Bongorian/mb4-independent-bass-bridge/revisions/B/pdf/MB4_design_and_drawings.pdf

# MB4 — 4弦独立サドルレス・ブリッジ

ジャズベ／プレベ想定。汎用M3ステンレス金物と、3種類の切削部品で構成。

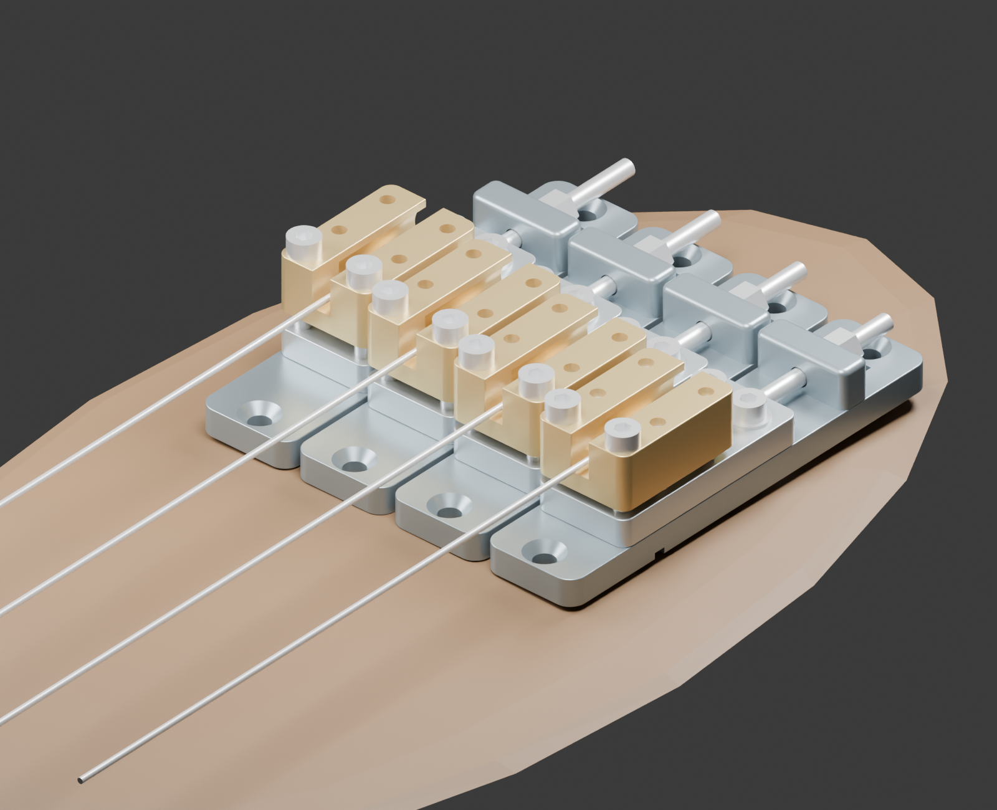
[picture p12: figure]

MB4 | Rev B | 2026-10-05 | 単位 mm | 試作・見積用 | 1 / 9

4個のモジュールを19 mmピッチで配置

ベース幅18 mm／全体幅75 mm

ベース奥行82 mm（ねじ棒は最大Y=90）

弦軸の参考高さ15〜20 mm

キャリッジ移動12 mm／各弦独立

裏面：φ12.5 × 深さ1.5のピエゾ用窪み

B01 固定ベース：A6061-T6 ×4

C01 キャリッジ：A6061-T6 ×4

A01 アンカー：C3604黄銅 ×4

外周R2〜R3／後壁上面R1。

3軸切削＋反転＋側面の穴加工。

M3ねじ穴はSTEPでは下穴径を表現。

図面のねじ指示を加工時に適用。

既存5穴には非互換。弦間・弦高・ボディ端までの余白を実機で確認して新規取付。

球状／筒状ボールの形・巻き方に応じて実弦で支点を確認。音質・分離度は未検証。

# B01 / 固定ベース

数量4 | A6061-T6 | 18 × 82 × 12、板厚5 | 外周R3、外周稜線R0.2、後壁は9ページ参照

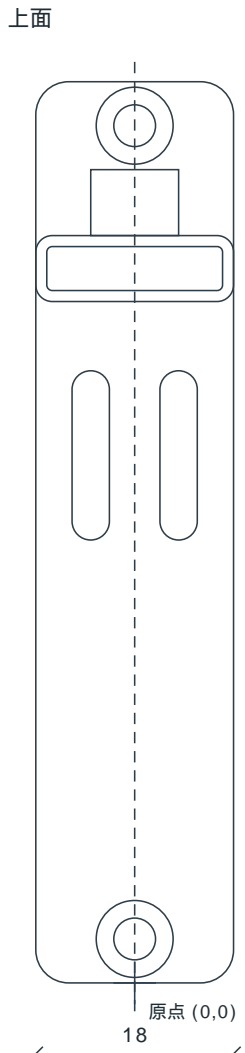
[picture p13: figure]
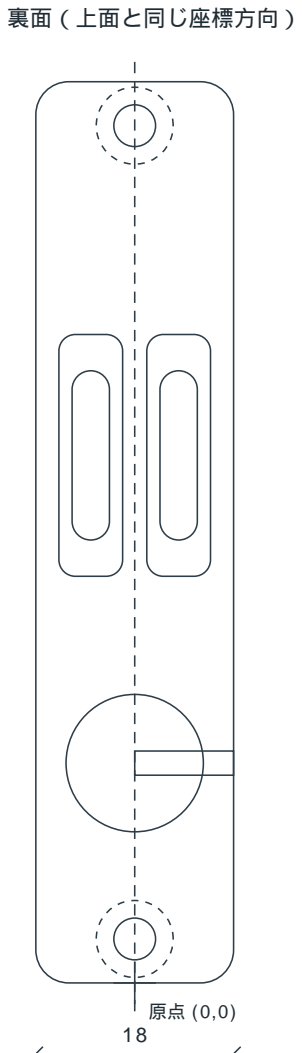
[picture p14: figure]
裏面（上面と同じ座標方向）

基準：X=幅中心、Y=前端、Z=ボディ面。

取付穴：(0,4)、(0,78)／φ3.8貫通。

皿座：上面φ7、90°、深さ1.6。

長穴中心：X=±4、Y=48。

長穴：幅3.4、全長15.4、貫通。

裏側ナット溝：5.8 × 22 × 深さ2.2。

同中心、四隅R1.5。裏面から切削。

ピエゾ窪み：(0,20)、φ12.5、深さ1.5。

配線溝：X=0〜9、Y=18.9〜21.1。

裏面から深さ1.2、右側面に開放。

後壁：Y=62〜68、Z=5〜12、幅18。

後壁穴：X=0、Z=7.5、φ3.4 Y方向貫通。

金物逃げ：X=±4、Y=68〜74。

上面から深さ1.5（底Z=3.5）。

側面（Y-Z）

82

# C01 / キャリッジ

数量4 | A6061-T6 | 18 × 40 × 5 | 外周R2、外周の上下稜線R0.2 | 穴位置・支持面高さは維持

上面

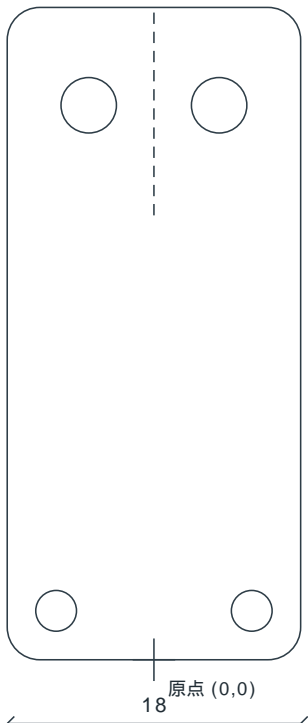
[picture p15: figure]

側面（Y-Z）

40

後面（X-Z）

基準：X=幅中心、Y=キャリッジ前端、Z=下面。

アンカー固定用：(±6,3)、M3 × 0.5 貫通、2箇所。

移動固定用：(±4,34)、φ3.4 貫通、2箇所。

後面ねじ：X=0、Z=2.5、Y方向 M3 × 0.5。

有効ねじ深さ10以上。φ2.5の円筒下穴深さ12＋ドリル先端0.75。

CADの後面穴は下穴形状。止めねじではなく張力受けのねじ棒を固定。

後面穴軸から上下面まで2.5。タップ後の残り肉は約1 mm。

ベース上の固定ねじ：M3 × 10 + 厚さ0.5ワッシャ + DIN562薄形四角ナット。

ナット5.5角 × 厚さ1.8。穴軸はベースのY=42〜54を移動。裏側溝に先にナットを入れる。

# A01 / ボールエンド・アンカー

数量4 | C3604快削黄銅 | 18 × 26 × 10 | 外周R2、外周上下稜線R0.2、スリット上縁R0.2

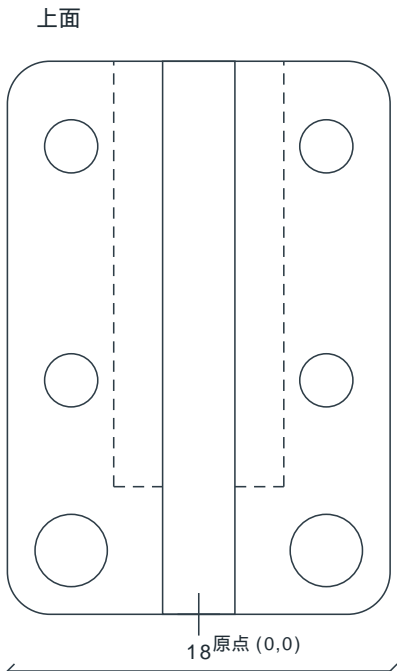
[picture p16: figure]

側面（Y-Z）

座面まで6

穴深さ20

後面（X-Z）

基準：X=幅中心、Y=前端、Z=下面。後面穴：X=0、Z=5、φ8、Y=26から深さ20。

開放スリット：幅3.4、全長26、底Z=3.3。上面から深さ6.7（R1.7端の工具逃げは部品外）。

高さ調整： (±6,11)、(±6,22)、4 × M3 × 0.5 貫通。保持ねじ：(±6,3)、2 × φ3.4 貫通。

ボールは後方から挿入し、Y=6の穴底肩で保持。弦は前方に水平に出す。後方穴は塞がない。

参考ボール外径6、厚さ4.75を仮定。最小厚さ3.8以上が条件。実弦で抜け・噛み込みを確認。

弦と巻き部分がスリット底・側壁に触れる場合はサドルレス条件が成立しない。最初の1個で検証。

# 組立断面・調整

弦高はネック／ボディの現物寸法と照合。弦を緩めて調整し、固定ねじは最後に締める。

中央模式図（Y-Z）：表示状態 q=14、g=2、参考弦軸H=17

← ナット側（前） | 後 →

ボディ面 Z=0

参考支点Y=q+6

裏面ピエゾの参考外形

窪みφ12.5 × 深さ1.5

参考素子φ12 × 厚さ0.7

接着・配線込みで1.2以下

金属面への短絡を防ぐ

ボディで素子を圧迫しない

前後調整：キャリッジ前端 q=8〜20。支点目安Y=14〜26。後ろのM3ナットで位置を合わせ、

四角ナットを使う上側2本のM3 × 10でキャリッジを固定。後ろの2個のナットをジャムロック。

高さ調整：4本のM3 × 10平先止めねじで隙間 g=0〜5。前後左右をそろえて、傾斜を抑える。

アンカー保持：2本のM3ボルトを下のキャリッジへ固定。底突きさせないため、次の金物を選ぶ。

g=0〜1未満：M3 × 16 + 厚さ1.0ワッシャ（0.5を2枚）。ねじ込み4〜5。

g=1〜3：M3 × 16、ワッシャなし。ねじ込み3〜5。

g=3超〜5：M3 × 20 + 厚さ2.0ワッシャ（0.5を4枚）。ねじ込み3〜5。

キャリッジの厚さは5。ボルト先端が下面を越えないことを組立時に確認。寸法公差分の余裕を取る。

# 部品表・加工指示

発注はB01／C01／A01の個別STEPとこのPDFをセットで。試作1弦分→実弦確認→4弦分が推奨。

B01 | 固定ベース A6061-T6 | | 18×82×12
C01 | キャリッジ A6061-T6 | | 18×40×5
A01 | アンカー C3604 | | 18×26×10
H01 | M3×10 平先 六角穴付き止めねじ SUS | 16 | 高さ調整
H02 | M3×16 六角穴付きボルト SUS | | アンカー保持 g<=3
H03 | M3×20 六角穴付きボルト SUS | 8予備 | アンカー保持 g>3
H04 | M3×10 六角穴付きボルト SUS | | キャリッジ固定
H05 | M3 DIN562 薄形四角ナット SUS | | 5.5角×厚さ1.8
H06 | M3全ねじ棒 SUS、長さ40 | | キャリッジへ10ねじ込む
H07 | M3六角ナット SUS | | 後面調整＋ジャムロック
H08 | M3平座金 φ7×厚さ0.5 SUS | 12 | 固定用8、後面用4
H09 | M3小形平座金 φ6×厚さ0.5 SUS | 32予備 | アンカー保持用の長さ合わせ
H10 | 3.5×20 皿木ねじ SUS | | 頭φ7以下／下穴は木部に合わせる
P01 | φ12以下・接着型ピエゾ接触センサ | 4別途 | 参考外形、品番未確定

一般公差：指定なし±0.10。ねじ位置・ボール穴・弦スリット・ナット溝は±0.05。

キャリッジ下面、ベース上面、アンカー下面は平面度0.05、Ra3.2以下を目標。

指定RはSTEPソリッドに実形状を反映。残る加工縁はC0.1以下でバリ取り、座面を損なわない。

ねじ山はSTEPで省略。ボール座肩は維持しバリのみ除去。初回は表面処理なし。R一覧は9ページ。

参考張力は1弦250 N、4弦1000 N。構造の設計目安で、強度試験・疲労試験を実施した値ではない。

# 取付テンプレート / 原寸 1:1

印刷は「実際のサイズ／100%」。50 mmチェック枠を定規で確認。既存穴との重なりも必ず確認。

75

E | A | D | G

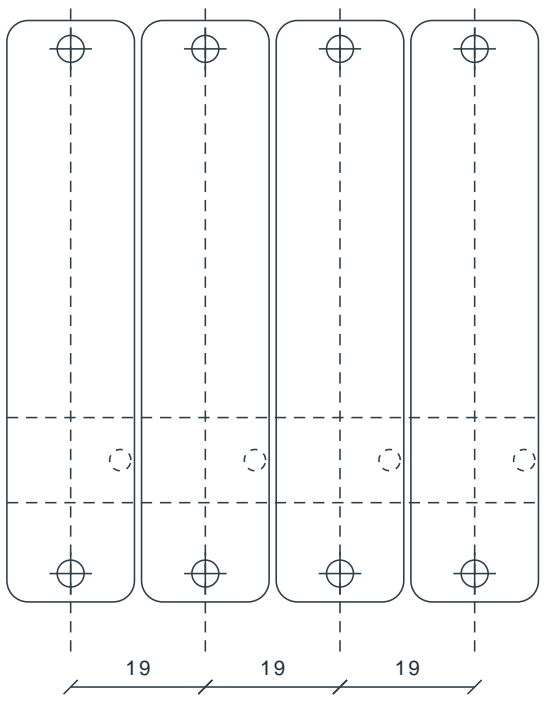
[picture p17: figure]

前端基準 Y=0：ナットから S−16 の位置を初期目安とする。

34インチ（S=863.6）なら 847.6 mm。実弦で補正位置を確認。

50 mm チェック枠

取付穴：各弦中心Xに2個

前側Y=4、後側Y=78

φ3.8は金属の通し穴径。

木部の下穴径は別途選ぶ。

破線丸：配線落とし穴の候補

各弦X+7、Y=20、φ3参考

配線溝下でボディ内へ引く。

位置・経路は内部配線を確認。

# 試作確認・ピエゾ配線・参照

これはCNC見積・試作を具体化する設計。特定のジャズベ／プレベへの取付保証は実測後に判断。

1. まず1弦分（B01/C01/A01各1個）を加工。ボールエンドの最大外形、抜け止め、巻き部分の

クリアランスを確認する。強い折れや弦の擦れ、隣の金物との干渉があれば設計寸法を修正する。

2. ボディ表面からの必要弦高を実測。15 mm未満が必要なら高さ寸法を再設計する。

既存ブリッジ穴と新規穴の距離・木部の厚さ・ボディ端までの余白を確認。下穴は木材に合わせる。

3. 木部への固定後、張力を徐々に上げる。キャリッジ、ボール、ねじの移動や緩みを確認する。

M3や黄銅タップは過大に締めない。必要締付力は現物と金物強度に基づいて決める。

4. オクターブは開放／12フレットで合わせる。巻き部分が振動する設計なので、弦銘柄と交換後に

音程・余韻を再確認する。メーカーが示す音質改善を本設計の保証として扱わない。

5. ピエゾは荷重を直接受けるサンドイッチ構造ではなく、裏面に接着する接触センサ。

φ12以下、配線・接着層を含む実装厚1.2以下を目安に、絶縁と0.3以上の木部クリアランスを確保。

セラミックの点荷重を避ける。振動伝達、接着位置、低域感度は実験で選ぶ。

6. E/A/D/G各ピエゾ → 各高入力インピーダンスのバッファ → 個別出力／ミキサー。

初期検討は入力1〜10 MΩ程度。低域の必要帯域と素子容量から決める。抵抗だけの直接並列接続は

各弦を独立に読み出せない。シールド・ストレインリリーフ・ブリッジアースも設ける。

7. 1本ずつ弾いた時の全4chを録音し、隣弦への混入を測る。固定ベース＋共通木部経由の機械的

クロストークは残る。MIDI等で強い分離が必要なら荷重経路に専用センサを置く設計へ変更する。

参照：Deviser “Ray Ross Bass Bridge (4Strings)” ／ サドルレス構造・調整の考え方。

https://www.deviser.co.jp/products/ray-ross-bass-bridge-4strings

PLOS ONE 2023, The acoustical behavior of a bass guitar bridge with no saddles, doi:10.1371/journal.pone.0292515

Accu HFSN-M3-A2（DIN562寸法）／ NBK 六角穴付き止めねじ寸法表（M3ピッチ0.5）。

# Rev B / R寸法と外観仕上げ

Rは表示用の平滑化ではなく、加工用STEPのソリッド形状に反映。外形の最大寸法と主要穴座標は維持。

B01 固定ベース：平面外形の四隅R3。板部分の外周上下稜線R0.2。

B01 後壁：平面外形の四隅R1.5、上面外周稜線R1。根元はベースと一体。

C01 キャリッジ：平面外形の四隅R2。外周の上下稜線R0.2。

A01 アンカー：平面外形の四隅R2。外周の上下稜線R0.2。

A01 開放スリット：長手方向の上側2本の縁にR0.2。最小幅3.4と底Z=3.3は維持。

ねじ頭の座面付近は小Rに抑え、大きな丸みで座面を削り込まない。

ボール保持肩Y=6、φ8穴、ねじ穴・長穴・ナット溝・ピエゾ窪みはRev Aと同じ。

接触平面のZ高さは維持。外周端だけを丸める。既存の金物と調整範囲を継続して使う。

加工：平面外周Rは通常の輪郭加工。稜線RはRカッター／ボールエンドミル等で仕上げる。

三次元の自由曲面・新しい旋盤部品は追加しない。工具経路と保持方法は加工業者が決定。

大Rの外形輪郭公差は±0.10、R0.2の稜線仕上げは±0.05を目安。指定Rは省略しない。

残る穴口・窪みの縁はC0.1以下でバリ取り。ボール保持肩と機能寸法を維持する。

2D図は小Rと側面Rの遷移を簡略表示。R一覧とSTEPの形状を合わせて加工する。

ソリッドの妥当性、STEP読戻し、9条件の部品・金物干渉、座面と機能穴の維持を確認。
