Bongorian/mb4-independent-bass-bridge/revisions/F/cad/reference/RevE_A04_anchor.step

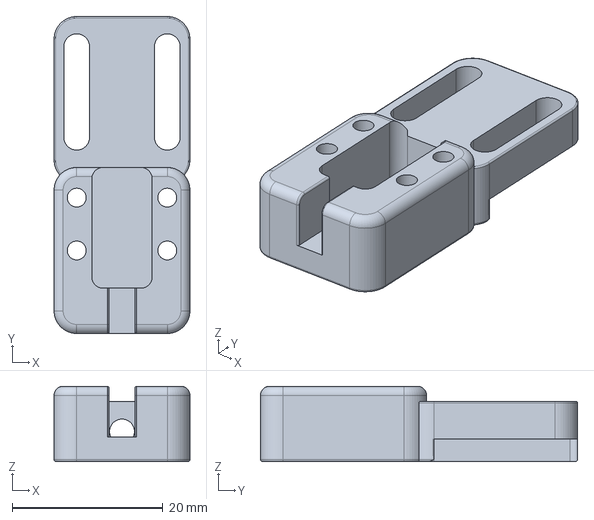
[picture p49: CAD file, 2026-10-05]
revisions/F/cad/reference/RevE_A04_anchor.step
18.0 x 42.0 x 10.0 mm
