Bongorian/mb4-independent-bass-bridge/revisions/F/MB4_mount_template_1to1.dxf

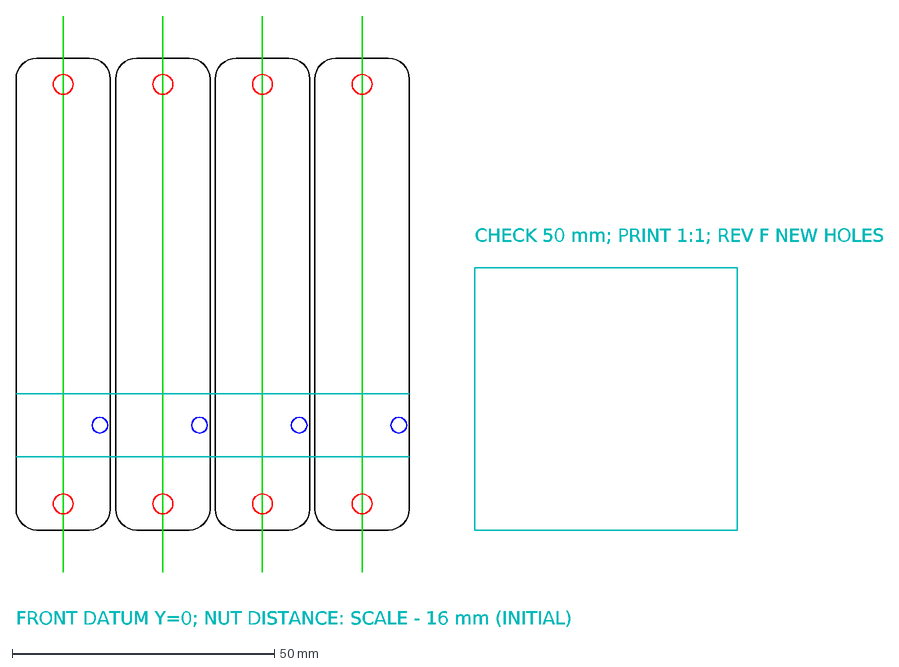
[picture p50: CAD file, 2026-10-05]
revisions/F/MB4_mount_template_1to1.dxf
CHECK 50 mm; PRINT 1:1; REV F NEW HOLES
FRONT DATUM Y=0; NUT DISTANCE: SCALE - 16 mm (INITIAL)
