Bongorian/mb4-independent-bass-bridge/revisions/G/cad/step/A06_smooth_anchor.step

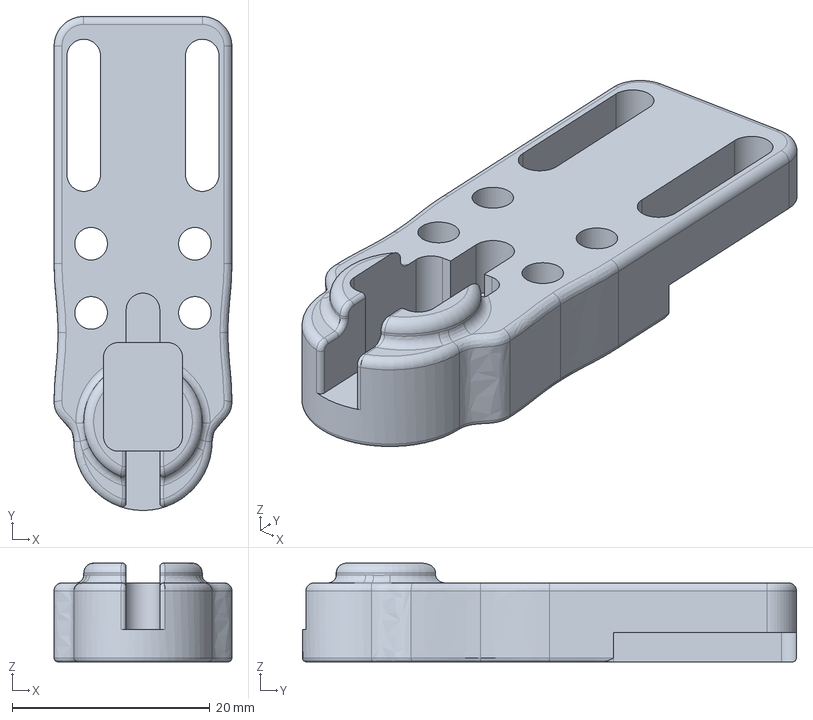
[picture p51: CAD file, 2026-10-05]
revisions/G/cad/step/A06_smooth_anchor.step
18.0 x 50.0 x 10.0 mm
