Bongorian/mb4-independent-bass-bridge/revisions/J/cad/step/A08_rounded_anchor.step

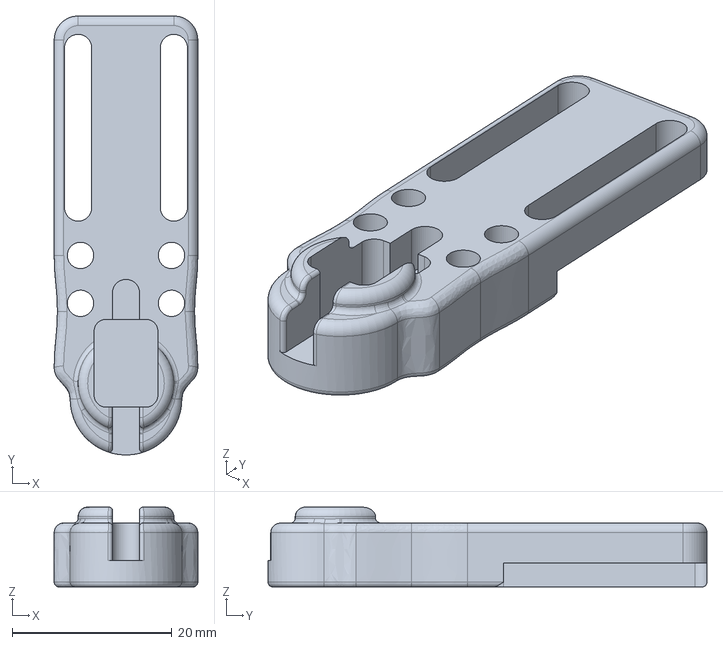
[picture p52: CAD file, 2026-10-06]
revisions/J/cad/step/A08_rounded_anchor.step
18.0 x 55.0 x 10.0 mm
