Bongorian/mb4-independent-bass-bridge/revisions/L/cad/step/B10_streamlined_base.step

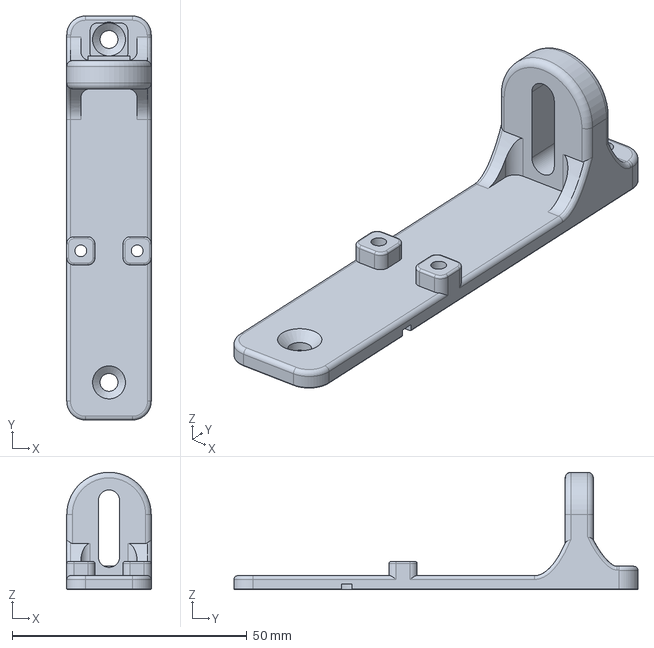
[picture p53: CAD file, 2026-10-07]
revisions/L/cad/step/B10_streamlined_base.step
18.0 x 86.0 x 25.0 mm
