Bongorian/mb4-independent-bass-bridge/revisions/L/MB4_mount_template_1to1.dxf

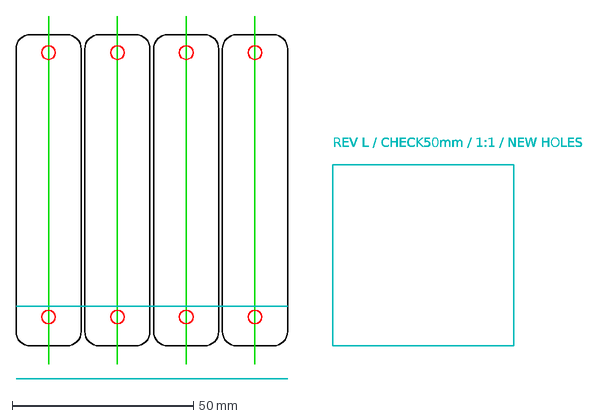
[picture p54: CAD file, 2026-10-07]
revisions/L/MB4_mount_template_1to1.dxf
REV L / CHECK50mm / 1:1 / NEW HOLES
