Bongorian/mb4-independent-bass-bridge/revisions/A/cad/step/A01_anchor.step

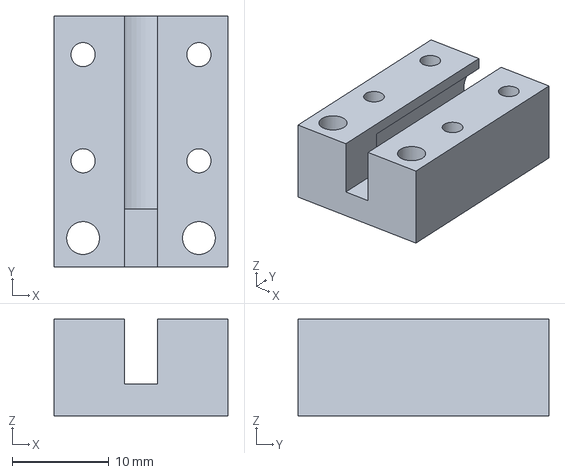
[picture p55: CAD file, 2026-10-05]
revisions/A/cad/step/A01_anchor.step
18.0 x 26.0 x 10.0 mm
