Bongorian/mb4-independent-bass-bridge/revisions/E/cad/step/B03_organic_base.step

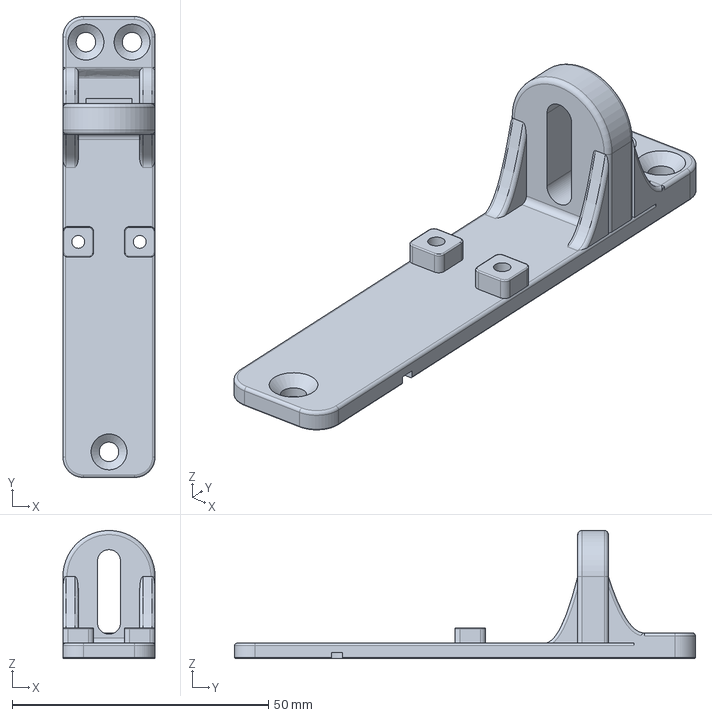
[picture p56: CAD file, 2026-10-05]
revisions/E/cad/step/B03_organic_base.step
18.0 x 90.0 x 25.0 mm
