Bongorian/mb4-independent-bass-bridge/revisions/G/cad/step/B05_smooth_base.step

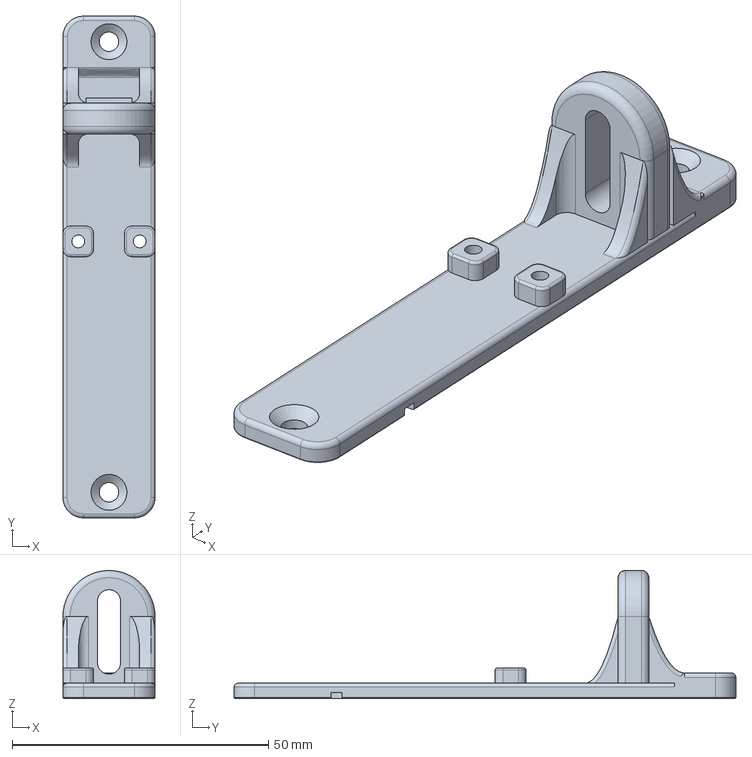
[picture p57: CAD file, 2026-10-05]
revisions/G/cad/step/B05_smooth_base.step
18.0 x 98.0 x 25.0 mm
