Bongorian/mb4-independent-bass-bridge/revisions/H/cad/step/B06_compact_base.step

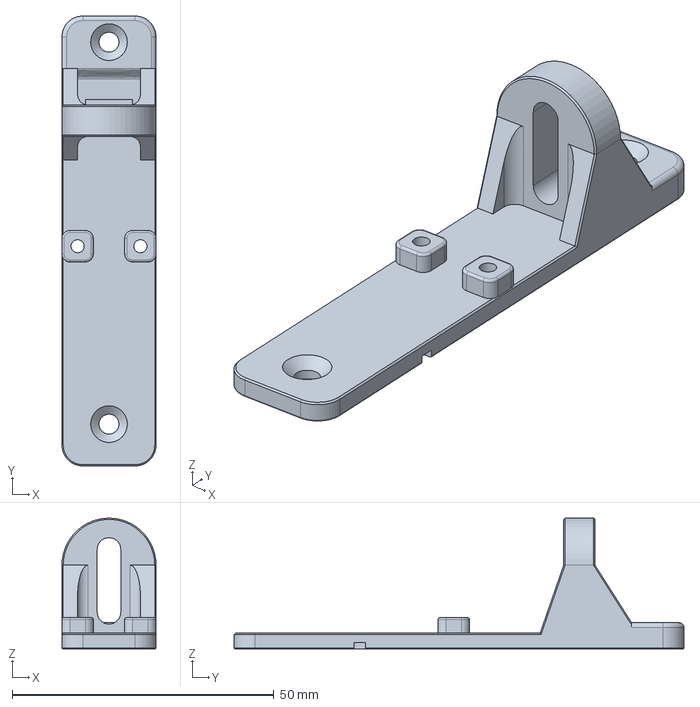
[picture p58: CAD file, 2026-10-05]
revisions/H/cad/step/B06_compact_base.step
18.0 x 86.0 x 25.0 mm
