Bongorian/mb4-independent-bass-bridge/revisions/B/cad/step/B01_base.step

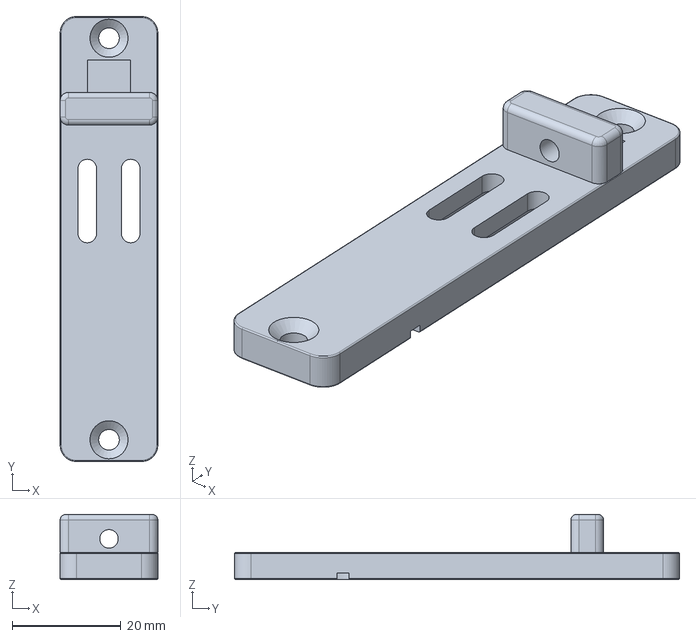
[picture p59: CAD file, 2026-10-05]
revisions/B/cad/step/B01_base.step
18.0 x 82.0 x 12.0 mm
