Bongorian/mb4-independent-bass-bridge/revisions/D/cad/step/A03_strengthened_anchor.step

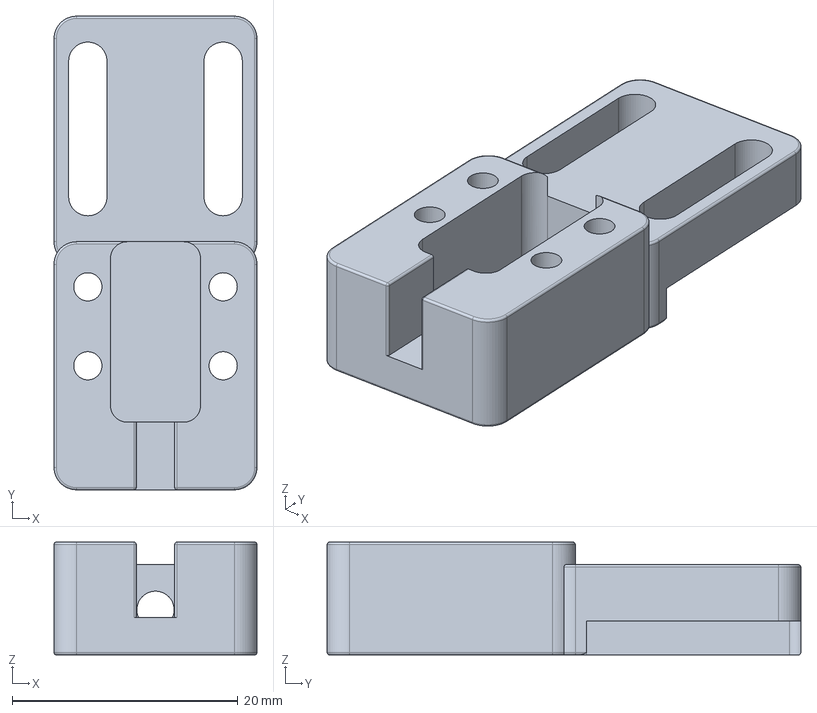
[picture p60: CAD file, 2026-10-05]
revisions/D/cad/step/A03_strengthened_anchor.step
18.0 x 42.0 x 10.0 mm
