Bongorian/mb4-independent-bass-bridge/revisions/F/cad/step/A05_crown_anchor.step

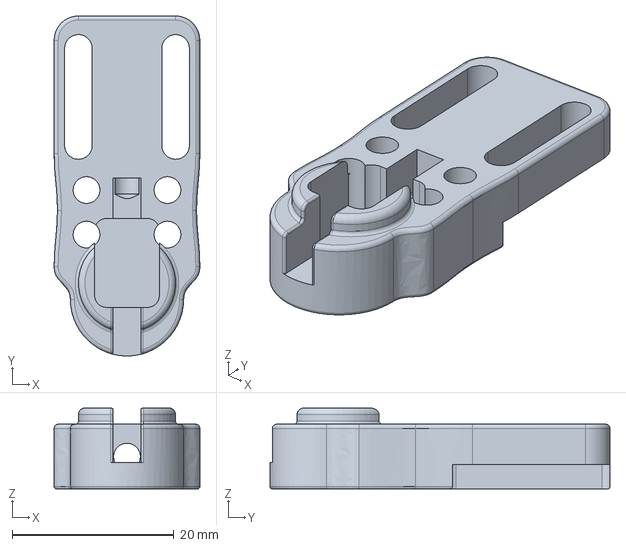
[picture p61: CAD file, 2026-10-05]
revisions/F/cad/step/A05_crown_anchor.step
18.0 x 42.0 x 10.0 mm
