Bongorian/mb4-independent-bass-bridge/revisions/J/cad/step/B08_rounded_base.step

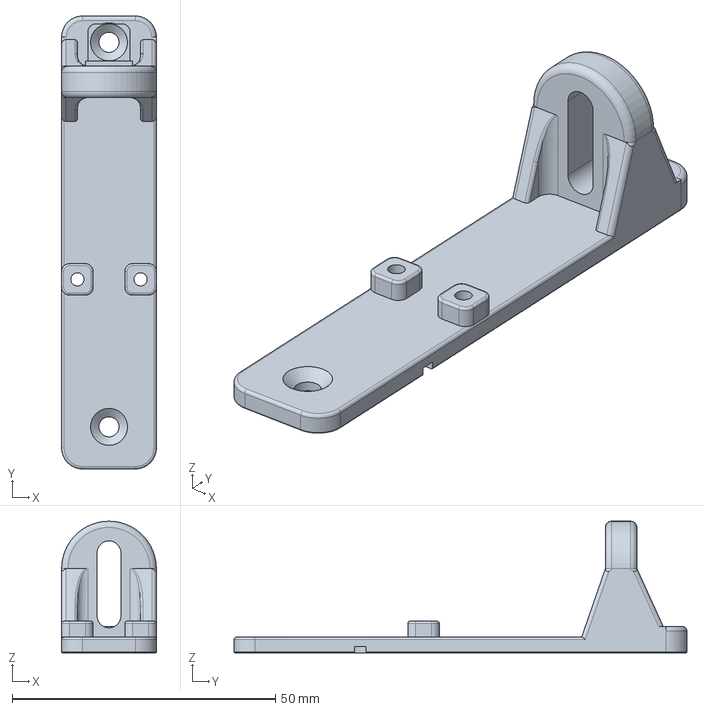
[picture p62: CAD file, 2026-10-06]
revisions/J/cad/step/B08_rounded_base.step
18.0 x 86.0 x 25.0 mm
