Bongorian/mb4-independent-bass-bridge/revisions/K/cad/step/A09_streamlined_anchor.step

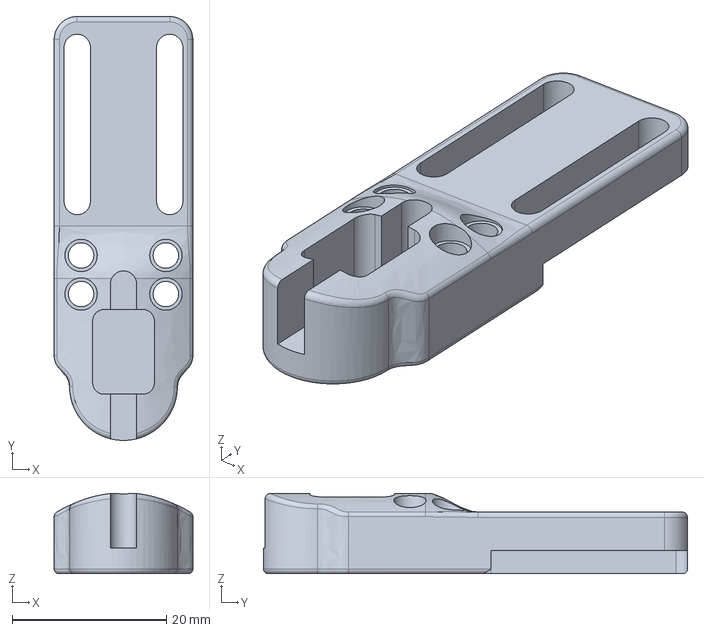
[picture p63: CAD file, 2026-10-06]
revisions/K/cad/step/A09_streamlined_anchor.step
18.0 x 55.0 x 10.4 mm
