Bongorian/mb4-independent-bass-bridge/revisions/K/pdf/MB4_RevK_guide.pdf

# MB4 / Rev K - 流線的な外形

丸い前部から低い後部へ滑らかにつなぐ。穴の入口を独立させ、20 mm調整・最低8 mmを維持。

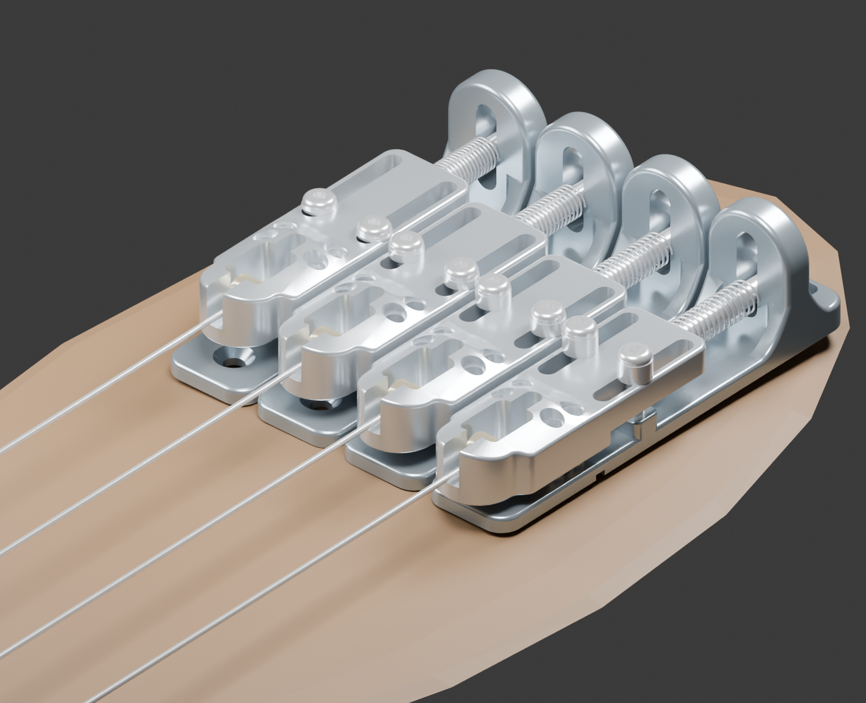
[picture p67: figure]

MB4 / REV K / 2026-10-06 / mm / PROTOTYPE - RFQ | 1 / 4

材質：6061-T6／両部品

ベース：18×86×25 mm

アンカー：18×55×最高10.5 mm

全幅：75 mm（弦間19）

連続調整：20 mm

アンカー前端q：-15〜5

参考弦中心：8〜20 mm

木ねじ：前1＋後1／弦

調整ボルト：M4×45 全ねじ

ばね：ミスミUY6-35

高さ調整：M4平先4本／弦

固定：低いM3ボタン頭2本

木ねじ位置・ピエゾはRev Hと同じ

最前位置ではアンカーがベース前端より15 mm張り出す。最前位置のモジュール全長は101 mm。

ベースを先にボディへ固定。球端・弦・ばね・ピエゾは参考外形。実機適合・耐久性は未検証。

# 20 mmの可動域 / 機構と成立条件

qはベース前端Y0から見たアンカー前端。固定M3を緩め、後方M4を回して連続調整する。

アンカー長穴：幅3.4、全長23.4。M3軸中心の移動は20 mm、端部に片側0.2 mm余裕。

固定パッドX±6/Y36、高さねじX±5.5/Y19・24。高さ穴の入口φ4.2、床Z8。

後壁Y70.5〜76.5は単純なR9アーチ。前後縁R1.2、リブは一続きの曲線。追加の座ボスはない。

短い後方タップ：全周ねじY47〜55の8 mm、裏開放窓Y25〜47につながる。

M4×45は全ねじ品を使用。半ねじSCB4-45では非ねじ部がアンカーへ入り、成立しない。

弦の肩; ばね作動長 30.5 mm / 前側張り出し 15 mm

ばね作動長 10.5 mm / 前側張り出し 0 mm

側面模式図

同倍率・寸法関係は

CADと一致。

丸みや金物の細部は

省略しています。

qの差：20 mm

肩の位置も20 mm移動。

# 汎用金物 / 公差と高さ調整

価格と在庫は注文時に確認。ミスミ参照URLとメーカー仕様を同梱。

前後：NBK SNSS-M4-45-FT（ミスミSNSS-M4X45-FT）。SUSXM7、全ねじM4×45、頭φ7×4。

ばね：UY6-35。SUS304-WPB、外径6、線径0.4、自由長35±1.5、ばね定数0.098 N/mm。

許容たわみ26.25、密着長参考6.8。作動長10.5〜30.5、最大公差時のたわみ26.0で範囲内。

最長の作動長30.5でも、短い個体の自由長33.5に対し3 mmの予圧が残る。

高さ：MSSFS4-8 / 12 / 16（平先、六角2）。固定：SSBCB3-12 / 16 / 20、25のみSBCB3-25。

座金：M3は外径6・厚0.5を積層。後方M4は外径8・厚0.5。木ねじは皿3.5×20候補。

隙間g | 参考弦中心 | 高さM4長さ | 固定M3長さ | 座金合計厚 | 先端Z
| | | 12 | 1.5 | 0.5
| 10 | | 16 | 3.5 | 0.5
| 12 | | 16 | 1.5 | 0.5
| 14 | 12 | 20 | 3.5 | 0.5
| 16 | 12 | 20 | 1.5 | 0.5
10 | 18 | 16 | 25 | 4.5 | 0.5
12 | 20 | 16 | 25 | 2.5 | 0.5

ベース固定を先に行う。後木ねじの皿頭座はZ3、逃げトレーは深さ2の上面開放加工。

組立後の後木ねじへの工具は調整ボルトと重なる。脱着時は先にアンカー・調整ボルトを外す。

CAD確認：全9端・中間条件で金物／部品／ばね包絡が干渉しない。4本の高さねじは全接地。

M4周囲の0.8 mm材料ガード、M3実下穴、STEP再読込を検証。荷重・疲労は実機で確認。

# 取付テンプレート / 1:1

100%印刷し、50 mm枠を実測。木ねじ穴とピエゾ位置はRev Hと共通。既存Jazz/Pの穴への互換は未確認。

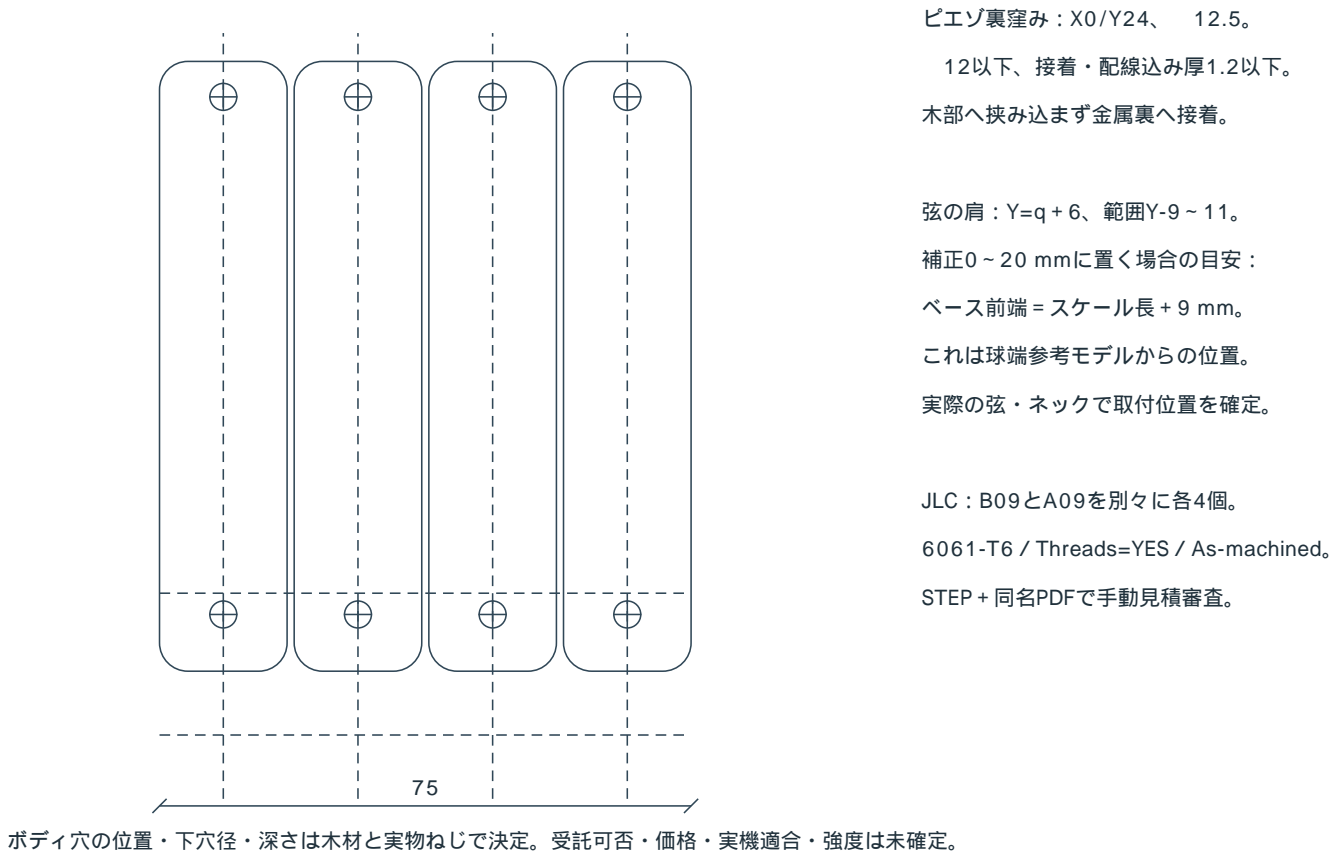
[picture p68: figure]
ピエゾ裏窪み：X0/Y24、φ12.5。; φ12以下、接着・配線込み厚1.2以下。; 木部へ挟み込まず金属裏へ接着。; 弦の肩：Y=q＋6、範囲Y-9〜11。; 補正0〜20 mmに置く場合の目安：; ベース前端＝スケール長＋9 mm。; これは球端参考モデルからの位置。; 実際の弦・ネックで取付位置を確定。; JLC：B09とA09を別々に各4個。; 6061-T6／Threads=YES／As-machined。; STEP＋同名PDFで手動見積審査。; ボディ穴の位置・下穴径・深さは木材と実物ねじで決定。受託可否・価格・実機適合・強度は未確定。

50 mm

取付穴：X=弦中心、Y8とY81。

前後の穴間距離73。通しφ3.8。

前後の皿座φ7/90°、頭座Z3。

後方はφ7.4深さ2の逃げを追加。
