Bongorian/mb4-independent-bass-bridge/revisions/H/pdf/MB4_RevH_guide.pdf

# MB4 / Rev H 短いベース・簡潔なリブ

前側の取付穴・ピエゾを後ろへ寄せ、ベースを12 mm短縮。弦間19 mm、各弦独立、4弦でCNC部品8点。

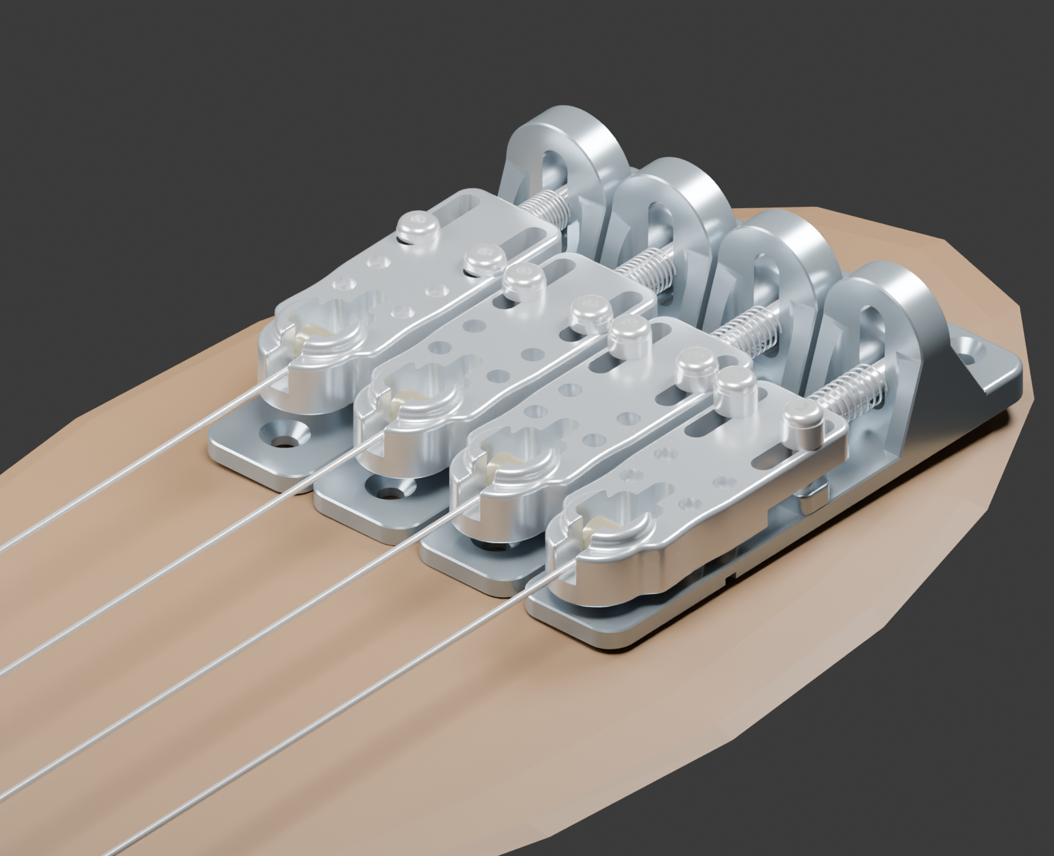
[picture p74: figure]

MB4 / REV H / 2026-10-05 / mm / PROTOTYPE - RFQ | 1 / 4

ベース・アンカー：6061-T6

ベース：18×86×25 mm

アンカー：18×50×最高10 mm

全幅：75 mm（弦間19）

参考弦中心：8〜20 mm

通常前後調整：10 mm

公称最大調整：12 mm

木ねじ：前1＋後1／弦

クラウン上縁R1.0、根元R0.8

リブは平面、内角R2／外縁C0.25

本体上縁R0.8、下縁R0.4

低いM3ボタン頭で固定

後方M4ネジ＋バネは継続

前木ねじはアンカーの下へ移動。ベースを先にボディへ固定し、後からアンカーを組む。

画像はCAD実形状。球端・弦・ばね・ピエゾは参考外形。実機適合と耐久性は試作で確認。

# 短縮とリブ整理 / 確認結果

アンカーA06はRev Gと同形状。ねじ・バネ・高さ調整範囲を保ち、ベースB06を変更。

Rev G → Rev H：前端を12 mm詰め、ベース長98→86。全幅75 mmは維持。

前木ねじ：旧版の同じ基準でY5→20、エンド側へ15 mm移動。

ピエゾ：旧版の同じ基準でY20→36、エンド側へ16 mm移動。

新版の前端をY0に取り直すため、新座標は前木ねじY8、ピエゾY24、後木ねじY81。

リブ上辺は直線、側面は平面。幅3と最高Z16を維持し、複雑な外縁の曲面Rを廃止。

内角R2は工具の逃げとして維持。外縁C0.25、根元とベース側面は連続した平面。

斜視図は隠れ線を省略して、見えている形を簡潔に表示。

CAD確認：STEP再読込、9組の高さ・前後位置で干渉なし。高さ・固定ねじを1201点確認。M3下穴の貫通も検証。

前木ねじの皿頭包絡とアンカーが干渉しないこと、アンカーなしで工具が入ることを確認。

前側を最大まで出すと、アンカー先端はベース前端より4 mm出る。通常範囲はq=-4〜6。

公称最大q=8はばねの実測が必要。参考弦中心8〜20 mm。実機適合・強度は未評価。

JLCへはB06/A06を別部品として各4個。Threads=YES、6061-T6、As-machined。

同名STEP＋英語PDFを添付。加工受託・工具到達性・価格は手動審査で確定。

前取付穴がアンカーの下へ移るため、組み付け後の取付穴への工具アクセスは想定しない。

参照：jlccnc.com/help/article/cnc-machining-ordering-guidelines

jlccnc.com/help/article/cnc-machining-design-guideline

jlccnc.com/help/article/aluminum-6061-cnc-machining

# 汎用金物と高さ調整

ミスミ型番は同梱のBOM・参照表を使用。ボタン頭の価格は購入時の見積で確認。

前後：SCB4-30（SUS、M4×30、ねじ部20／首下の非ねじ10）＋UY6-20＋小形M4座金。

高さ：MSSFS4-8 / 12 / 16（平先、六角2）。gに合わせて4本／弦を交換。

固定：SSBCB3-12 / 16 / 20、長さ25だけSBCB3-25。頭径5.7、高さ1.65、六角2。

座金：WSJS-SUS-M3（外径6、厚0.5）。高さに合わせて合計厚を選択。

SCB3-12/16/20/25のキャップ頭は同じ首下長で代替可能。価格と納期を比較する。

木ねじ：コノエ270011003520候補（SUS皿3.5×20）。頭径7以下／90°を現物確認。

ピエゾ：各弦φ12以下。接着・配線込み厚1.2以下。木部へ挟み込まず金属裏へ接着。

| 参考弦中心 | 高さM4長さ | 固定M3長さ | 座金合計厚 | 先端Z
| | | 12 | 1.5 | 0.5
| 10 | | 16 | 3.5 | 0.5
| 12 | | 16 | 1.5 | 0.5
| 14 | 12 | 20 | 3.5 | 0.5
| 16 | 12 | 20 | 1.5 | 0.5
10 | 18 | 16 | 25 | 4.5 | 0.5
12 | 20 | 16 | 25 | 2.5 | 0.5

固定先端はZ0.2〜0.7、木部への突出を避ける。公差を含め実測し座金で調整。

ばね自由長20±1.5、許容たわみ15。作動長13−q >= 実測自由長−15。

通常q=-4〜6の10 mmを推奨。q=8までの12 mmは実測ばねが条件を満たす場合のみ。

弦を緩めて高さ・前後を調整し、固定M3を締める。4本の高さねじを均等に当てる。

# 取付テンプレート / 1:1

100%で印刷。50 mmチェック枠を実測。Rev H専用、新規穴あけ用。既存Jazz/Pの穴とは非互換。

50 mm

取付穴：X=弦中心、Y8とY81。

各モジュールの前後穴間距離73。

金属側通し穴φ3.8、皿φ7/90°。

ボディ穴の位置・深さは実測して決定。

木ねじの下穴径は木材と実物ねじから選ぶ。

既存穴・裏の空洞・木部端を避ける。

弦を受ける肩：Y=q＋6。

通常Y2〜12、公称最大Y14。

初期の前端位置目安：スケール長−4。

実弦の補正量を確認して位置を確定。

ピエゾ裏窪み中心：各弦X0/Y24。

配線は窪みから右側面へ逃がせる。

共通の木部による弦間振動は残る。

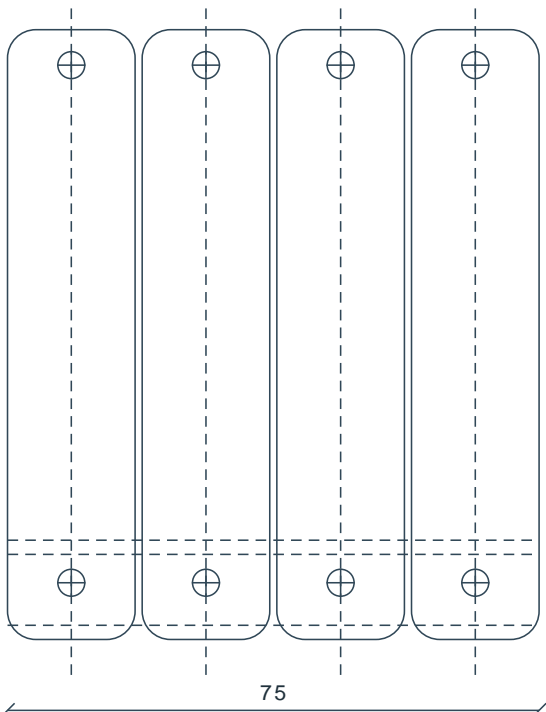
[picture p75: figure]

組立順：ベース固定 → 配線 → アンカー・ばね・調整ねじ。前木ねじの頭は完全に皿座へ収める。
