Bongorian/mb4-independent-bass-bridge/revisions/E/pdf/qa/page-07.png

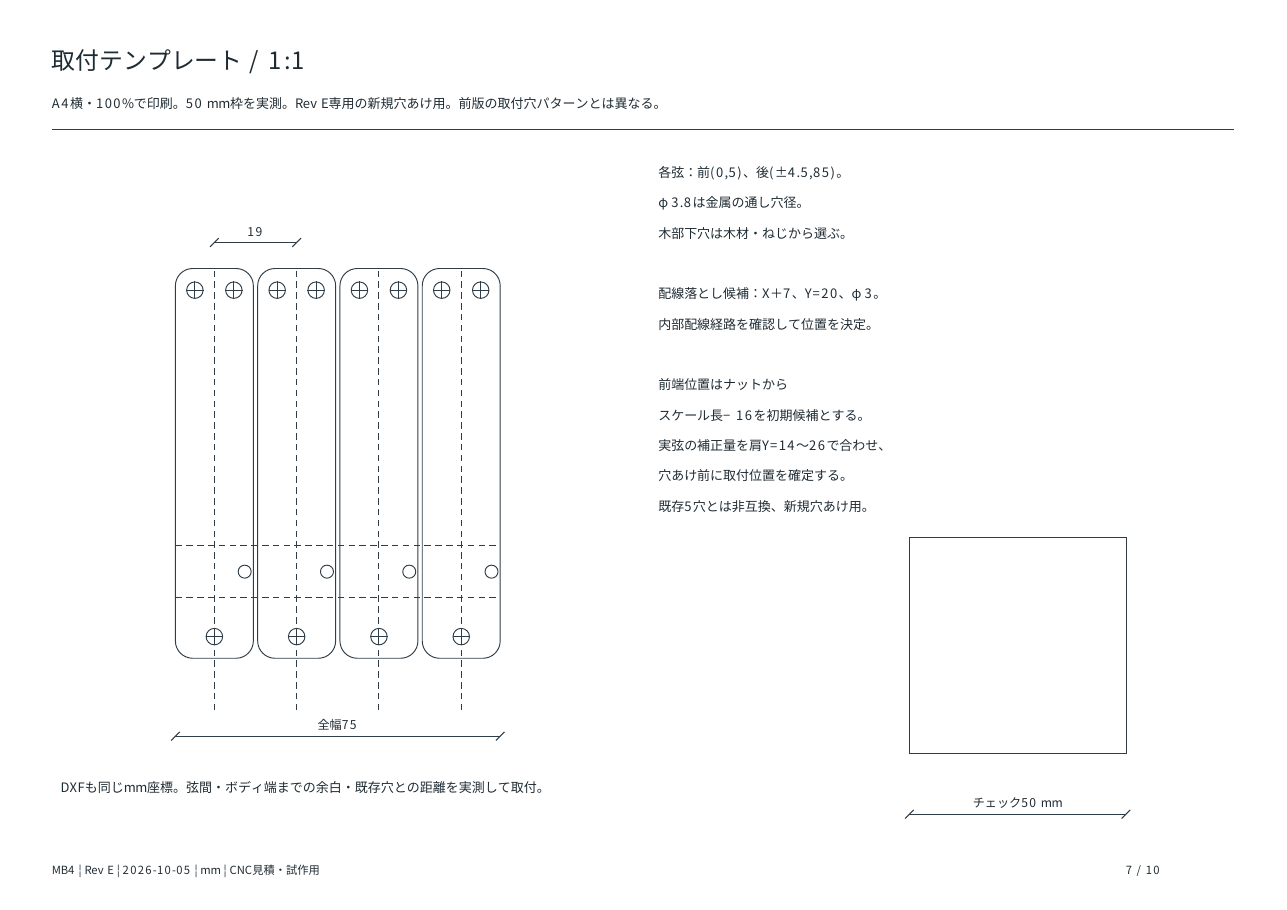
revisions/E/pdf/qa/page-07.png
