Bongorian/mb4-independent-bass-bridge/revisions/D/cad/section_scan.csv

rev | z | area_mm2 | centroid_y | Ixx_mm4 | section_modulus_mm3 | nominal_bending_MPa
C | 3.6 | 107.14159265359721 | 69.99999999999993 | 317.35176877782214 | 105.78392292593821 | 47.644290933780375
D | 3.6 | 147.97182431244005 | 69.73602555301508 | 1234.7347245790297 | 188.91216299015915 | 28.53177855086428
C | 3.8 | 107.14159265359721 | 69.99999999999993 | 317.35176877782214 | 105.78392292593821 | 46.9825646708112
D | 3.8 | 146.5124552149748 | 69.75575605063821 | 1200.791097066016 | 185.04770484931942 | 28.74934333463886
C | 4.0 | 107.14159265359721 | 69.99999999999993 | 317.35176877782214 | 105.78392292593821 | 46.32083840784203
D | 4.0 | 145.5700059803341 | 69.76569261792062 | 1171.433739855769 | 182.11571960270751 | 28.827824481341192
C | 4.2 | 107.14159265359721 | 69.99999999999993 | 317.35176877782214 | 105.78392292593821 | 45.65911214487286
D | 4.2 | 144.87000598033404 | 69.77101583789262 | 1144.4479895872064 | 179.6335182186211 | 28.83648915507926
C | 4.4 | 100.24811747774761 | 69.99999999999997 | 296.67134325014194 | 98.89044775004638 | 48.13407268648723
D | 4.4 | 144.17000598033408 | 69.77630982738305 | 1117.9712321436964 | 177.18454176682283 | 28.839987670734995
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
