Bongorian/mb4-independent-bass-bridge/revisions/E/cad/section_scan.csv

rev | z | area_mm2 | centroid_y | Ixx_mm4 | section_modulus_mm3 | nominal_bending_MPa
D | 3.6 | 147.9718243124713 | 69.73602555301572 | 1234.734724579961 | 188.91216299027678 | 28.531778550846514
E | 3.6 | 180.6177566968064 | 70.57334716317013 | 3197.253301410936 | 339.1716362993793 | 15.89165903967974
D | 3.8 | 146.5124552150064 | 69.75575605063887 | 1200.7910970669473 | 185.04770484943782 | 28.749343334620463
E | 3.8 | 178.5904708539579 | 70.64911925827148 | 3094.576343974448 | 330.939554931 | 16.075443145831287
D | 4.0 | 145.570005980366 | 69.76569261792127 | 1171.4337398567004 | 182.11571960282737 | 28.82782448132222
E | 4.0 | 177.22508998099494 | 70.70719982469566 | 3011.91789651406 | 324.11305605246343 | 16.19805158095882
D | 4.2 | 144.8700059803664 | 69.7710158378933 | 1144.4479895881377 | 179.63351821874184 | 28.836489155059876
E | 4.2 | 176.20641101983693 | 70.75492330620581 | 2942.0785548974527 | 318.2319217588697 | 16.27743681831197
D | 4.4 | 144.17000598036674 | 69.77630982738373 | 1117.9712321445113 | 177.18454176692626 | 28.83998767071816
E | 4.4 | 175.26740632877622 | 70.79852771362198 | 2879.5269818122033 | 312.9419793809406 | 16.328905473495638
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
