Bongorian/mb4-independent-bass-bridge/revisions/F/JLC_thread_wall_issue.png

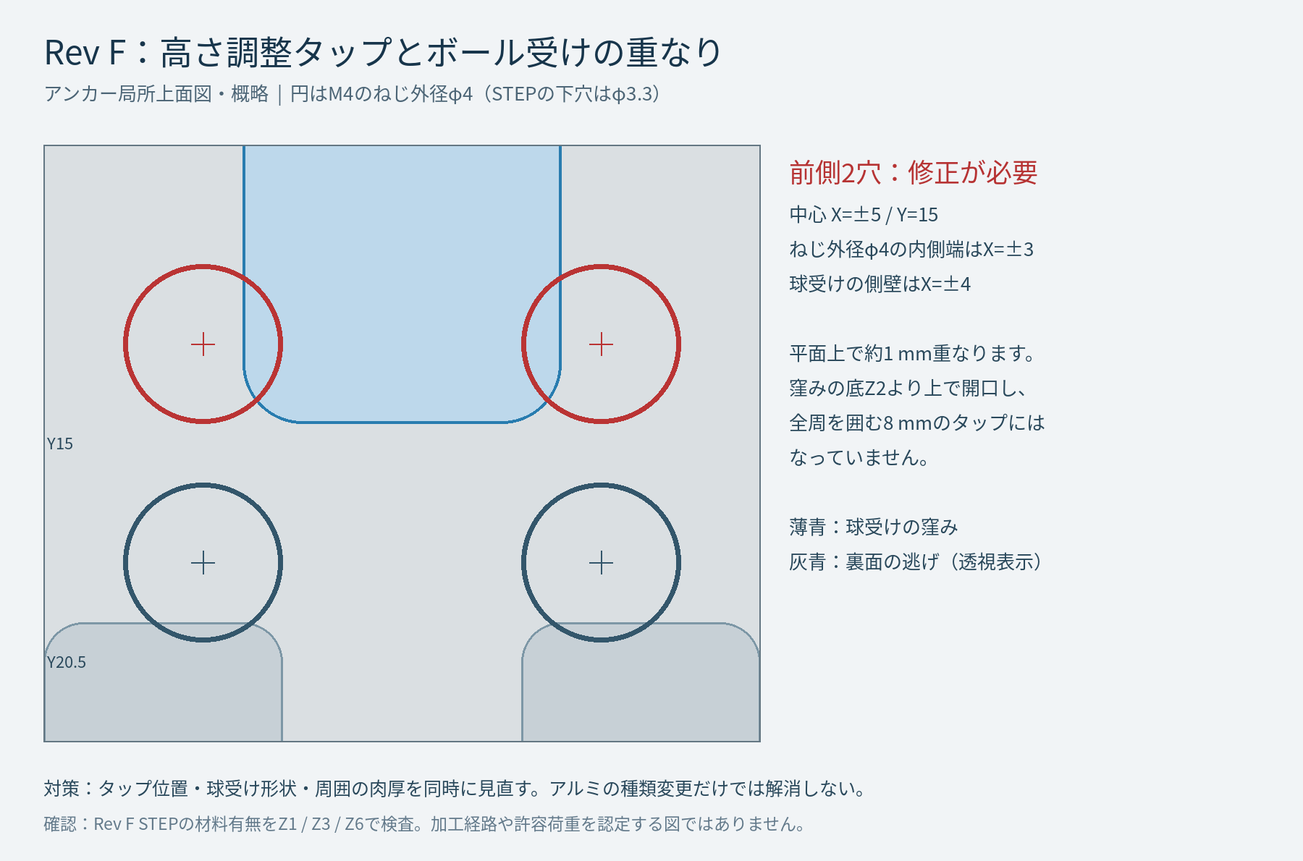
revisions/F/JLC_thread_wall_issue.png
