Bongorian/mb4-independent-bass-bridge/revisions/J/travel_preview.png

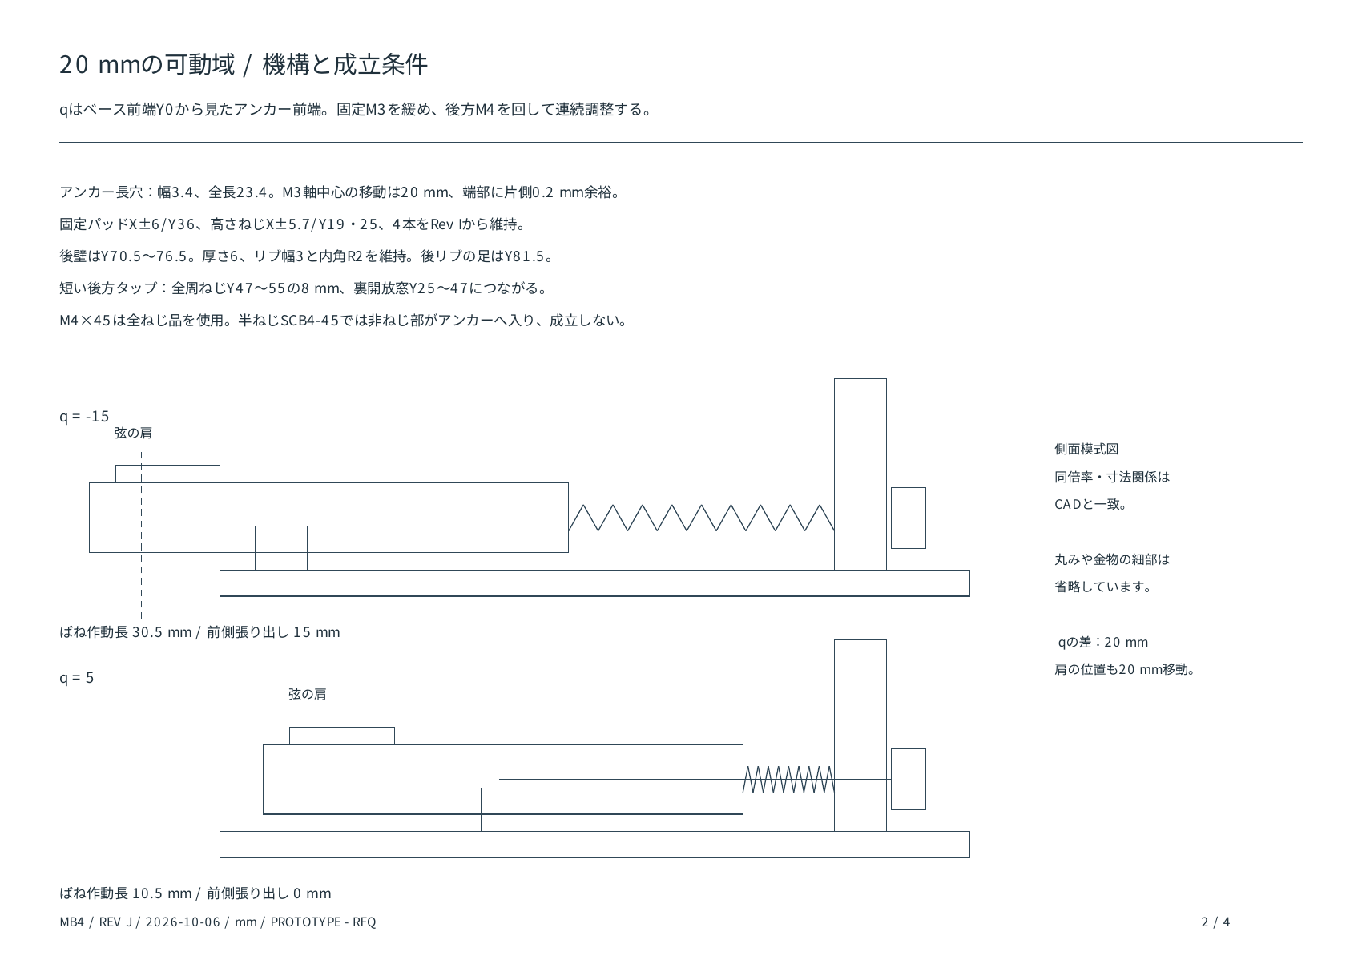
revisions/J/travel_preview.png
