Bongorian/mb4-independent-bass-bridge/revisions/L/bridge_rear_preview.png

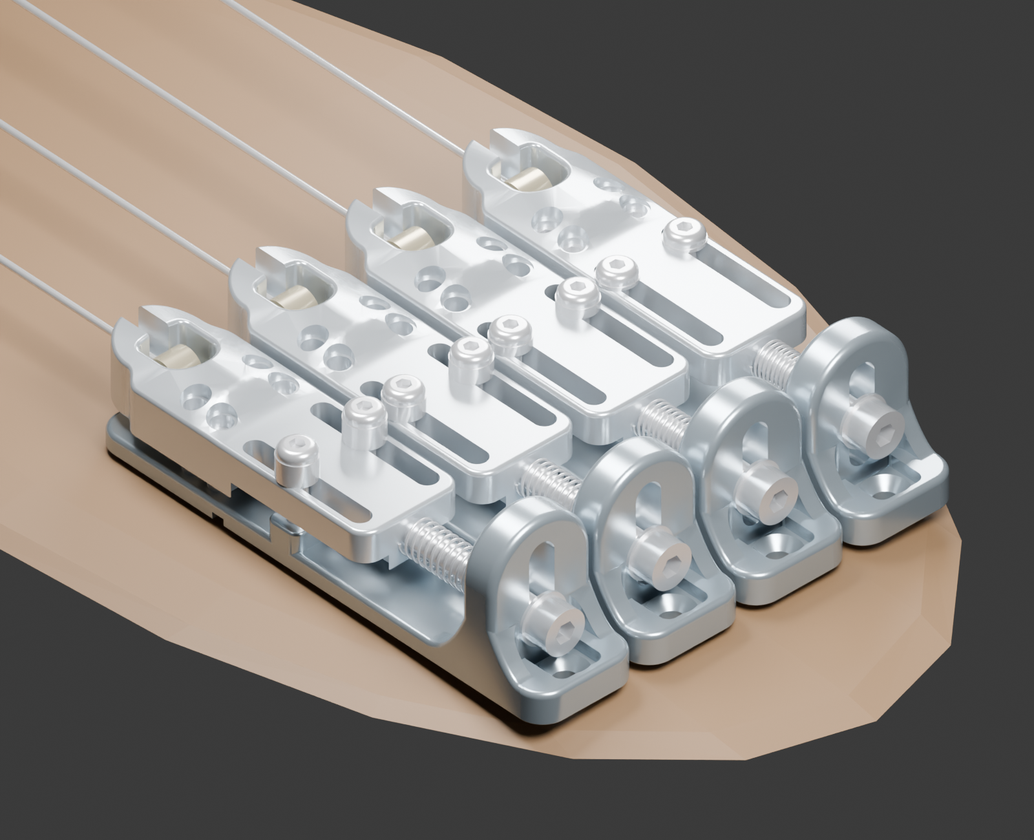
revisions/L/bridge_rear_preview.png
