Bongorian/mb4-independent-bass-bridge/revisions/L/six_views/03_left.png

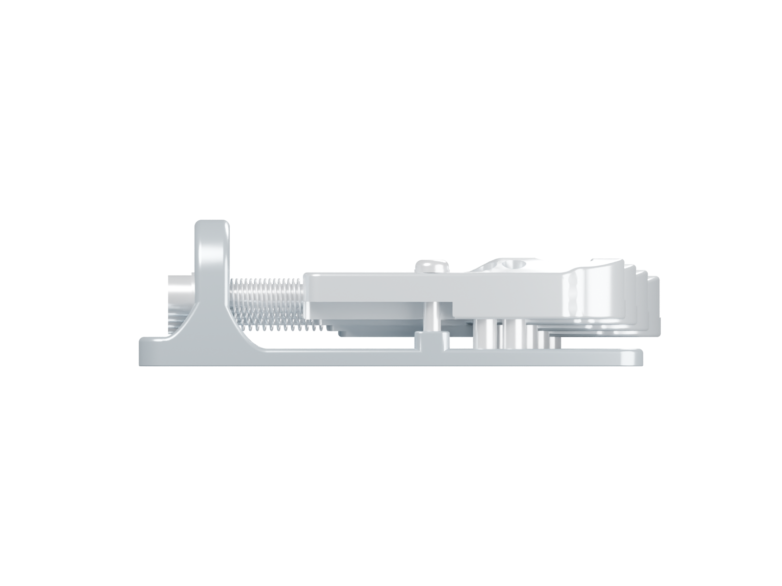
revisions/L/six_views/03_left.png
