Bongorian/mb4-independent-bass-bridge/revisions/L/six_views/06_bottom.png

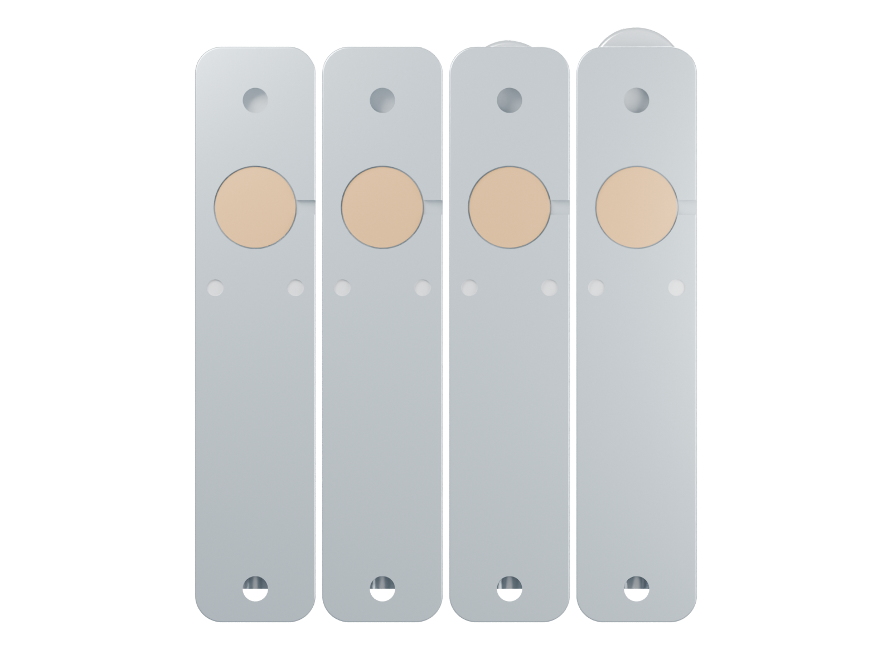
revisions/L/six_views/06_bottom.png
